RBSC/iBolit2/Board/iBOLIT.bmp

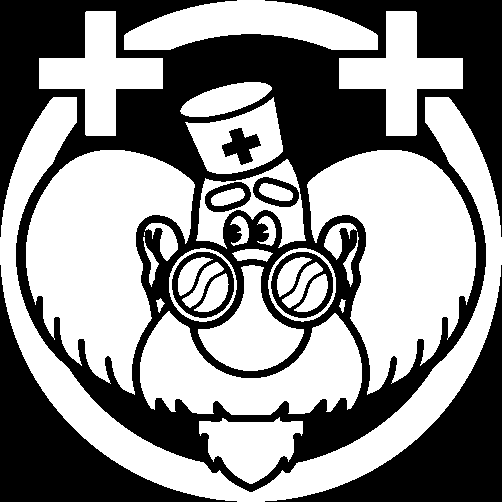
Board/iBOLIT.bmp
