RBSC/iBolit2/Pics/Board_front.png

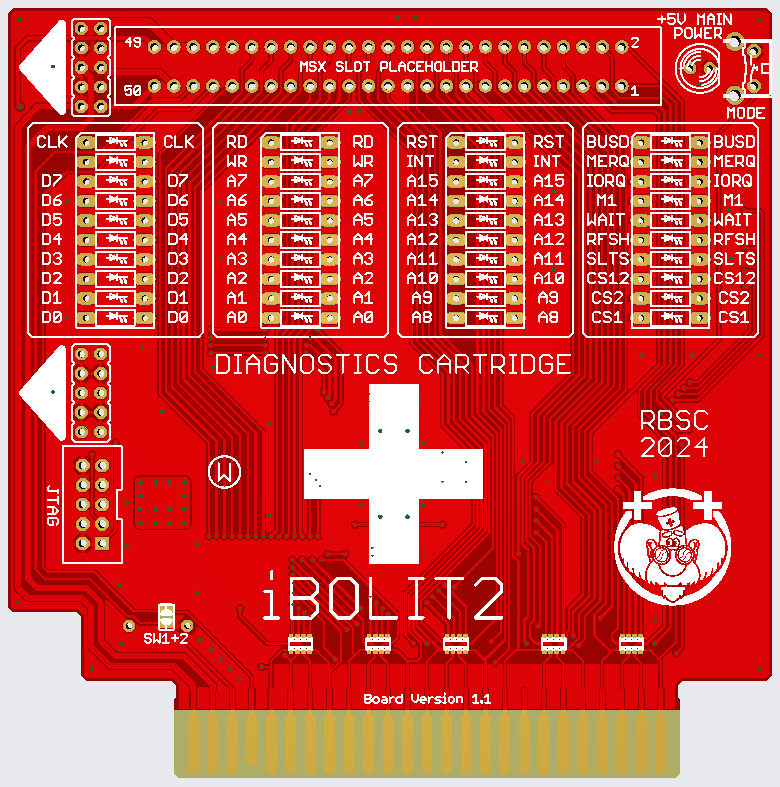
Pics/Board_front.png
