RBSC/iBolit2/Pics/Daughterboard_back.png

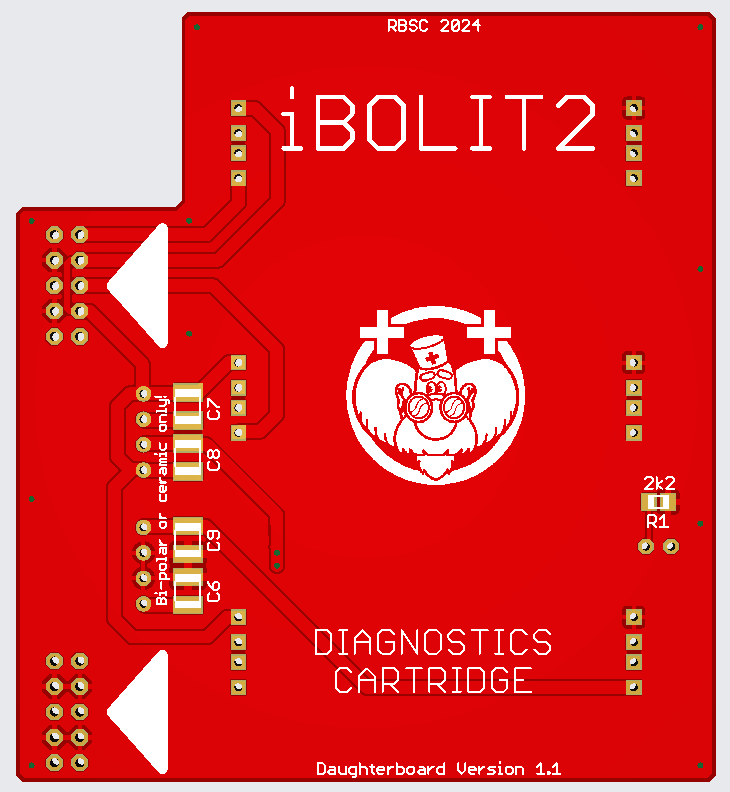
Pics/Daughterboard_back.png
