RBSC/iBolit2/Pics/iBolit2_top.jpg

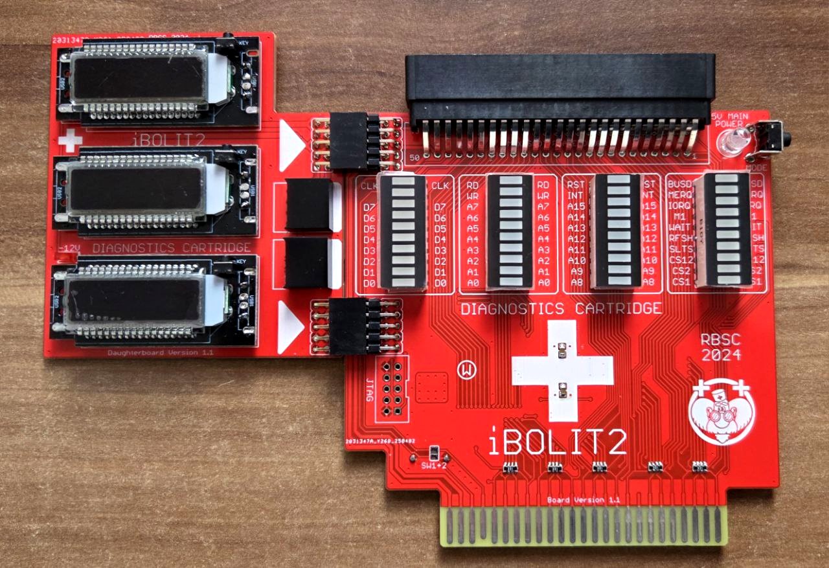
Pics/iBolit2_top.jpg
